arturs-lab/basis108/commercial_version/applefritter/resources/oldcomputer.info/revw.pdf

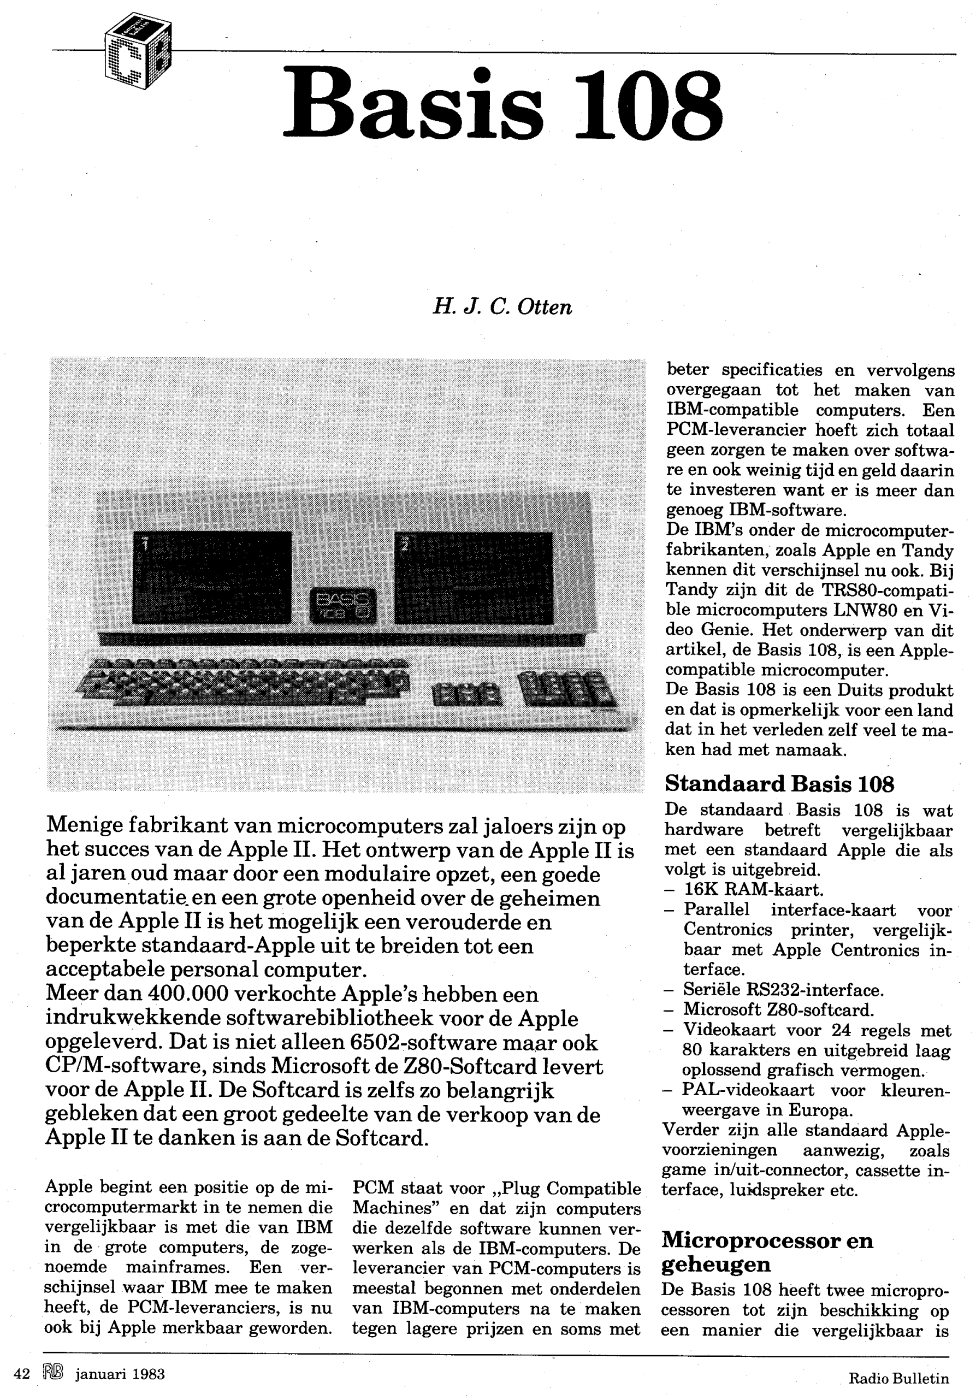
[picture p13: figure]

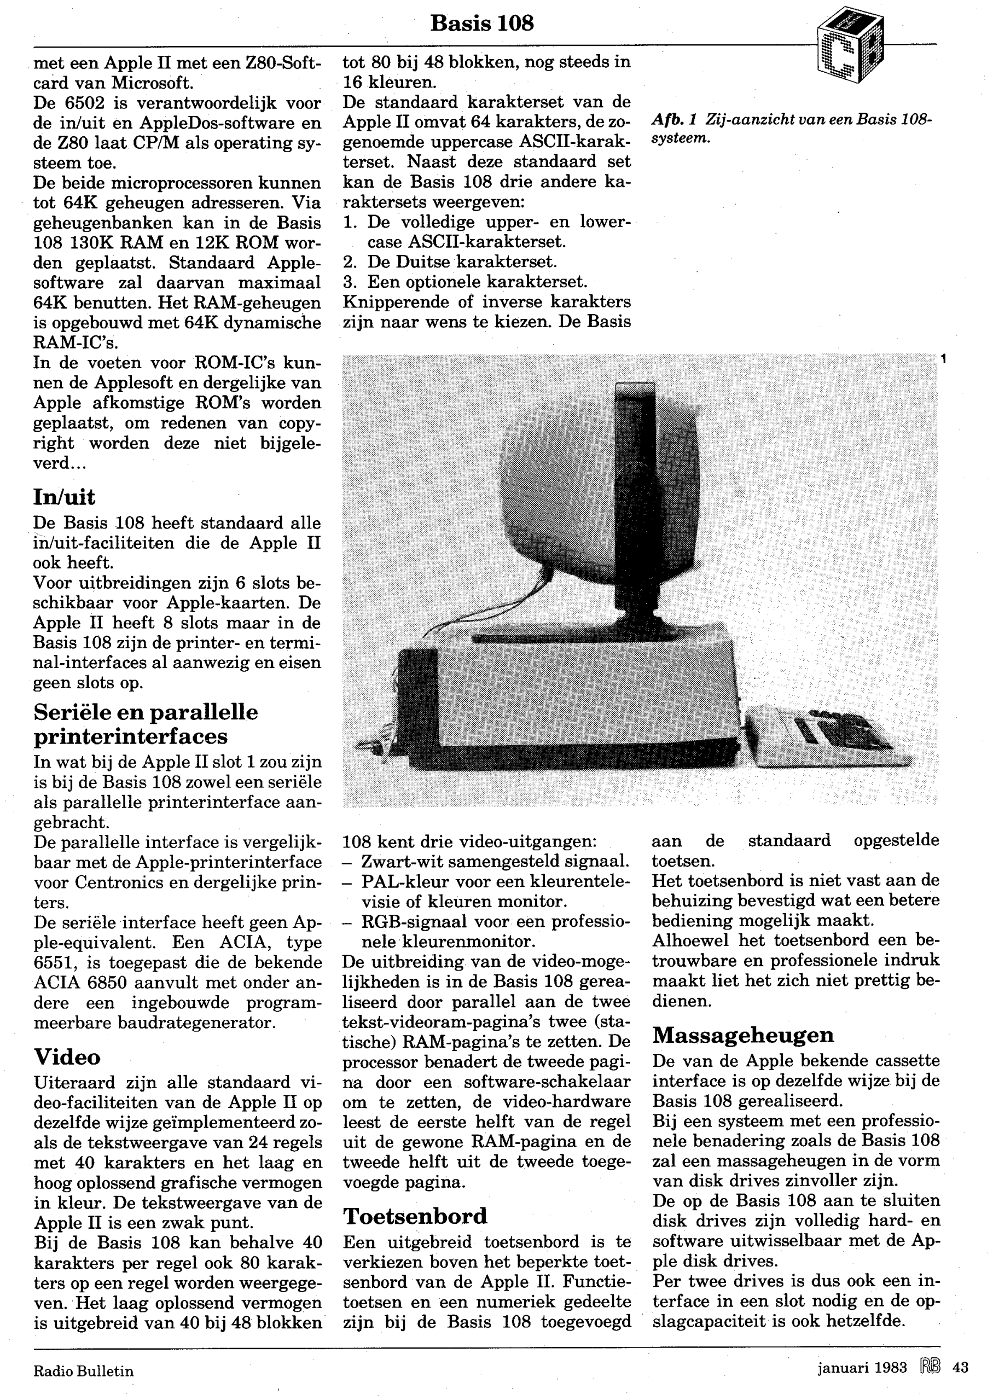
[picture p14: figure]

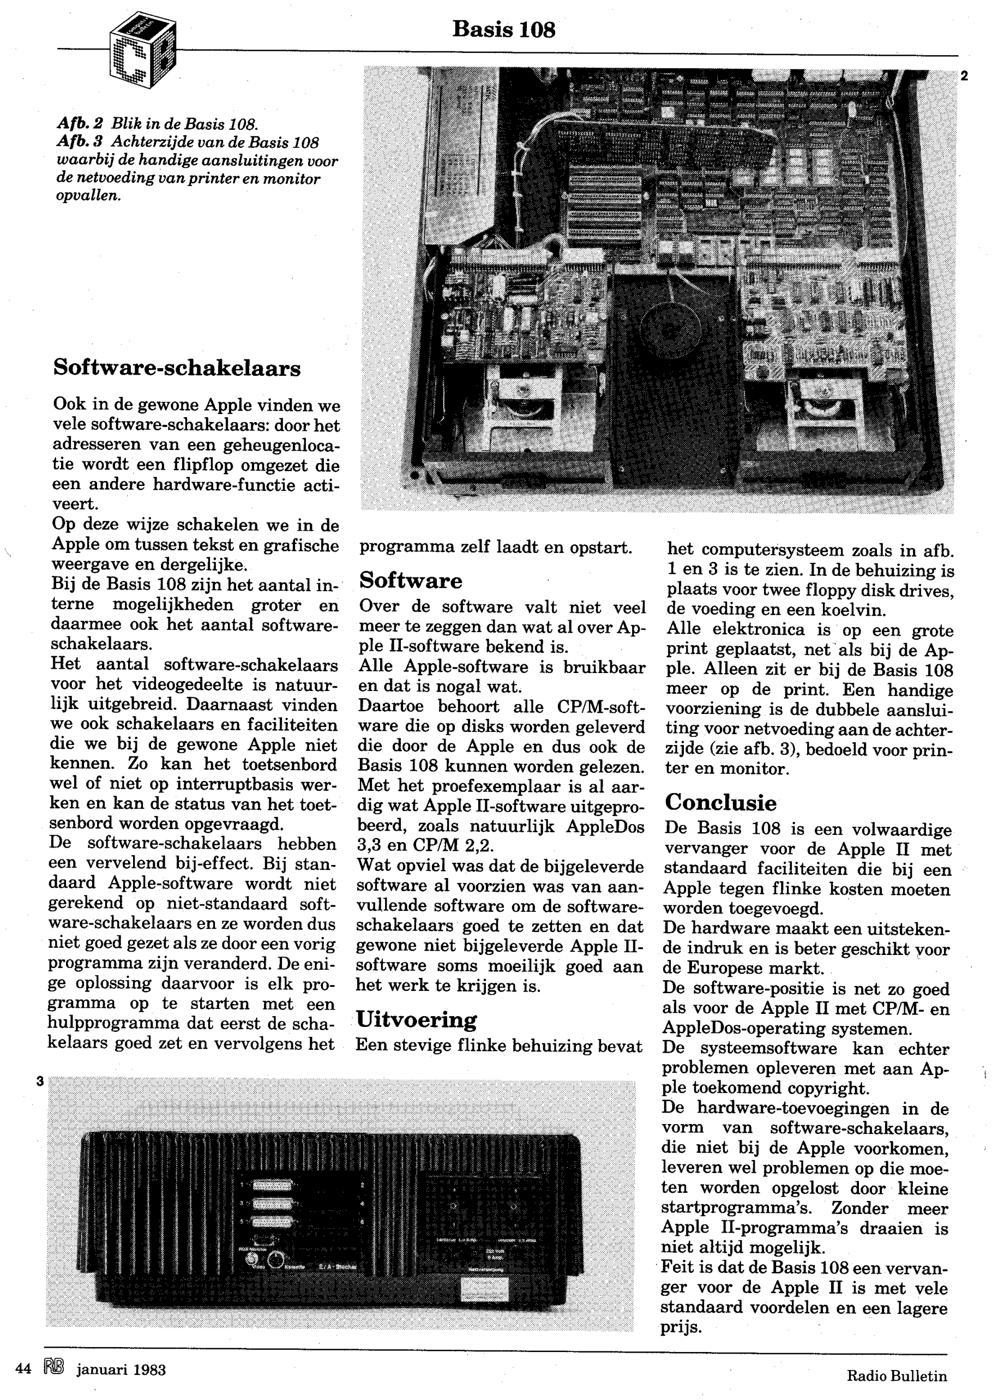
[picture p15: figure]
