arturs-lab/basis108/commercial_version/applefritter/Basis 108 Clone _ Applefritter_files/b108_07.JPG

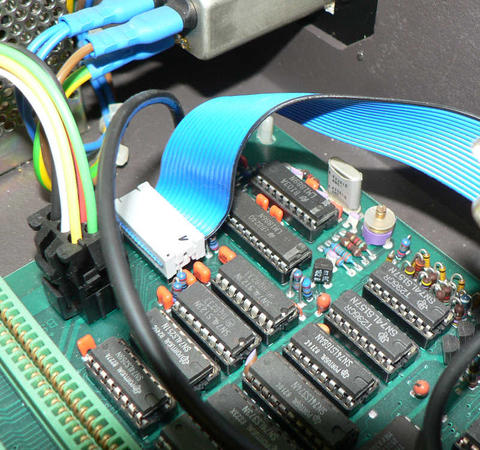
commercial_version/applefritter/Basis 108 Clone _ Applefritter_files/b108_07.JPG
