arturs-lab/basis108/commercial_version/applefritter/Basis 108 Clone _ Applefritter_files/Basis-108-EPROMs_and_Switch_0.jpg

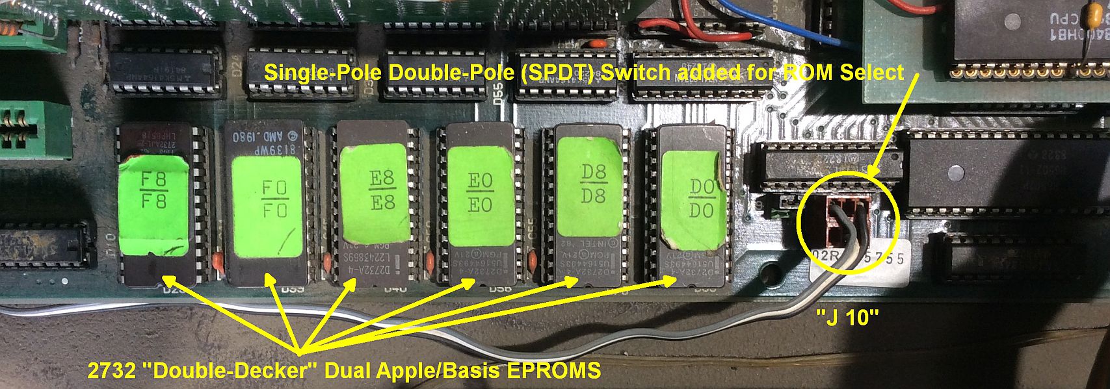
commercial_version/applefritter/Basis 108 Clone _ Applefritter_files/Basis-108-EPROMs_and_Switch_0.jpg
