arturs-lab/basis108/commercial_version/applefritter/Basis 108 Clone _ Applefritter_files/Basis-108-Interior-All-Ann1.jpg

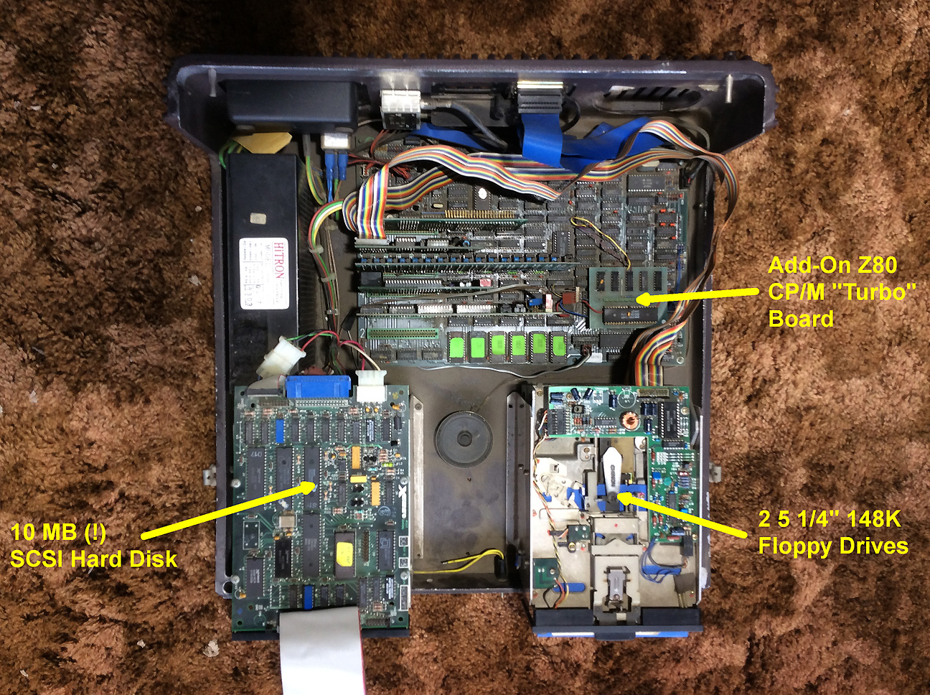
commercial_version/applefritter/Basis 108 Clone _ Applefritter_files/Basis-108-Interior-All-Ann1.jpg
