arturs-lab/basis108/commercial_version/images/FB_IMG_1675830168287.jpg

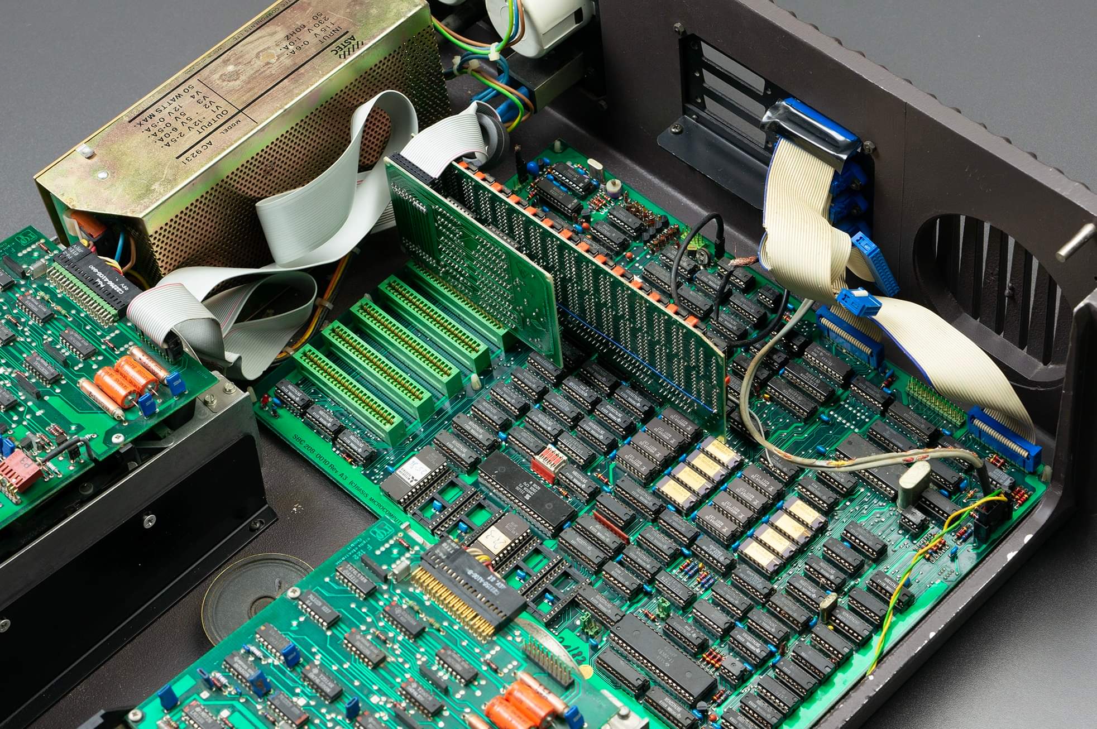
commercial_version/images/FB_IMG_1675830168287.jpg
