arturs-lab/basis108/commercial_version/images/FB_IMG_1675830313314.jpg

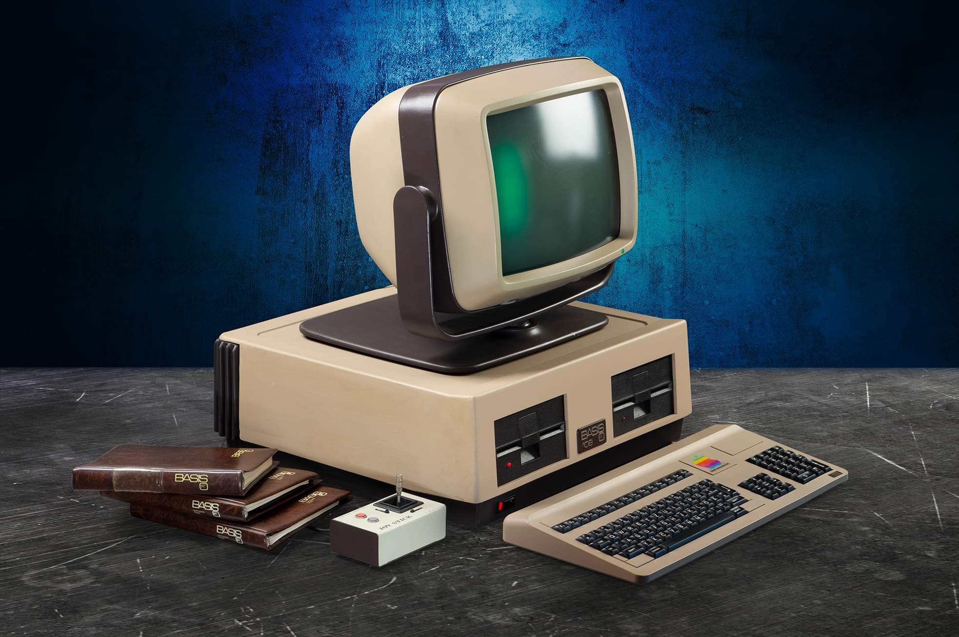
commercial_version/images/FB_IMG_1675830313314.jpg
