arturs-lab/basis108/commercial_version/images/FB_IMG_1675830322174.jpg

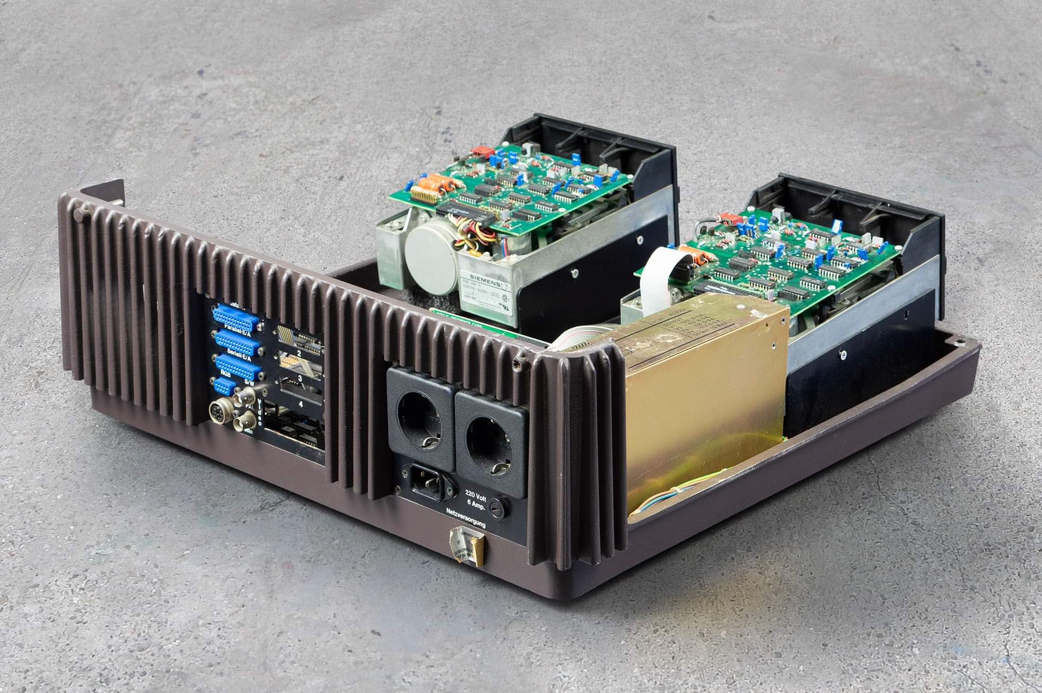
commercial_version/images/FB_IMG_1675830322174.jpg
