arturs-lab/basis108/floppy_controller/AppleBox - Ehring FDC4 Diskcontroller_files/FDC4Bild.jpg

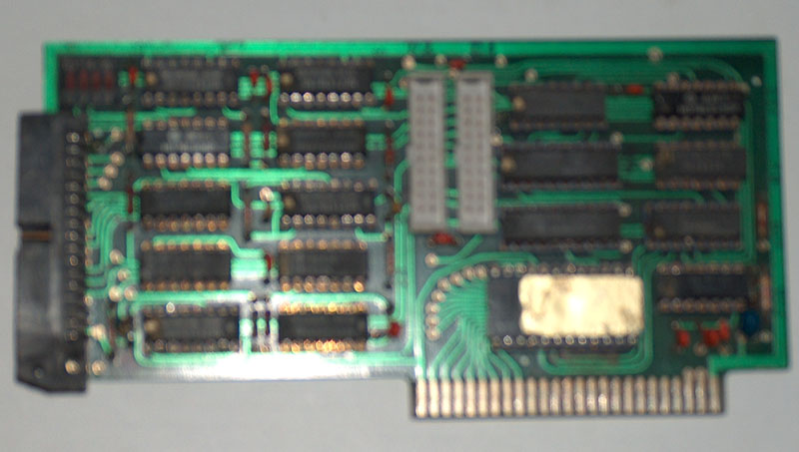
floppy_controller/AppleBox - Ehring FDC4 Diskcontroller_files/FDC4Bild.jpg
