arturs-lab/basis108/floppy_controller/AppleBox - Ehring FDC4 Diskcontroller_files/FDC4Schaltplan.jpg

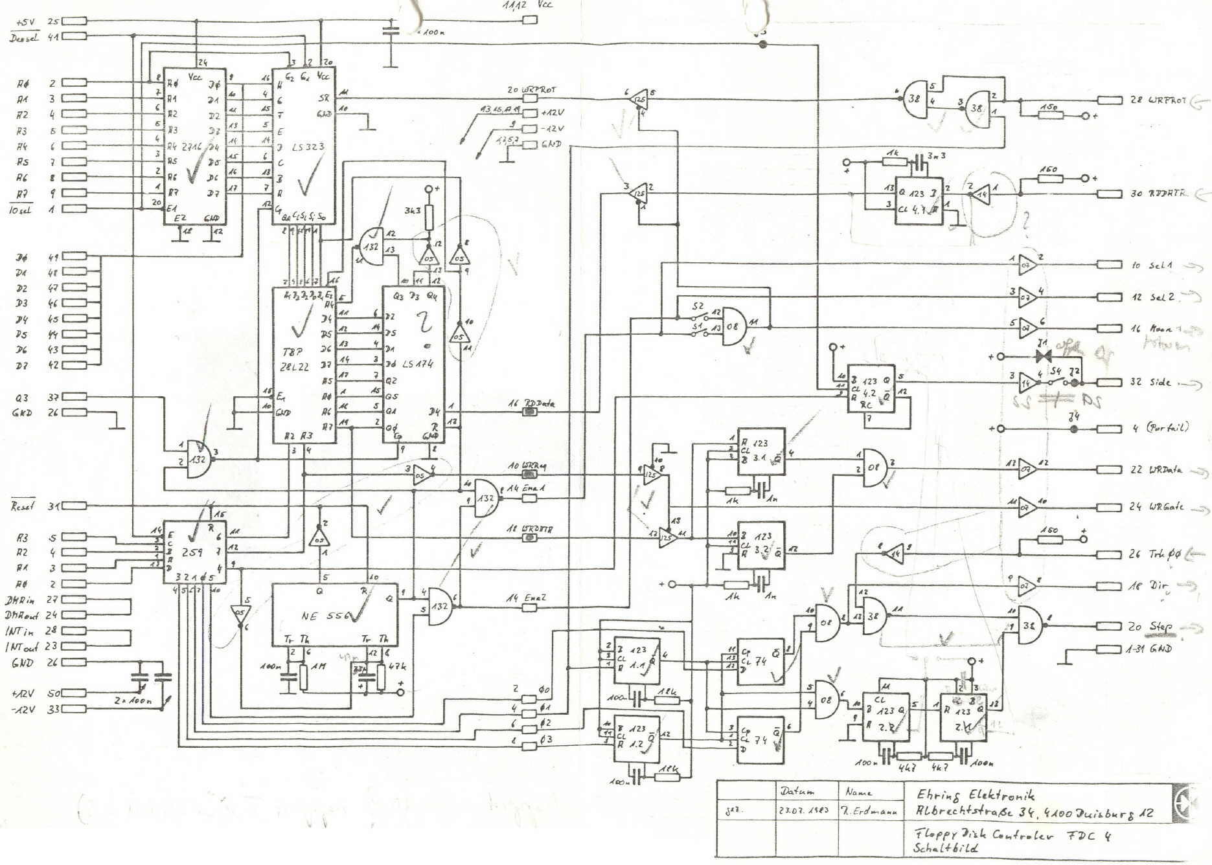
floppy_controller/AppleBox - Ehring FDC4 Diskcontroller_files/FDC4Schaltplan.jpg
