arturs-lab/basis108/floppy_controller/AppleBox - Ehring FDC4 Diskcontroller_files/page004.jpg

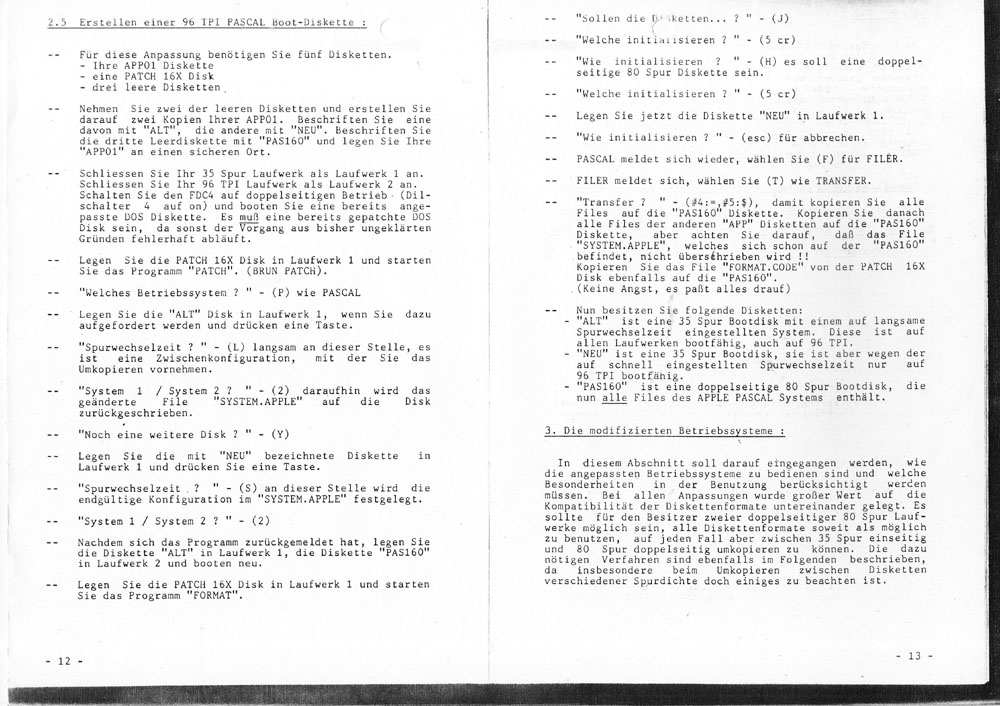
floppy_controller/AppleBox - Ehring FDC4 Diskcontroller_files/page004.jpg
