arturs-lab/basis108/floppy_controller/AppleBox - Ehring FDC4 Diskcontroller_files/page014.jpg

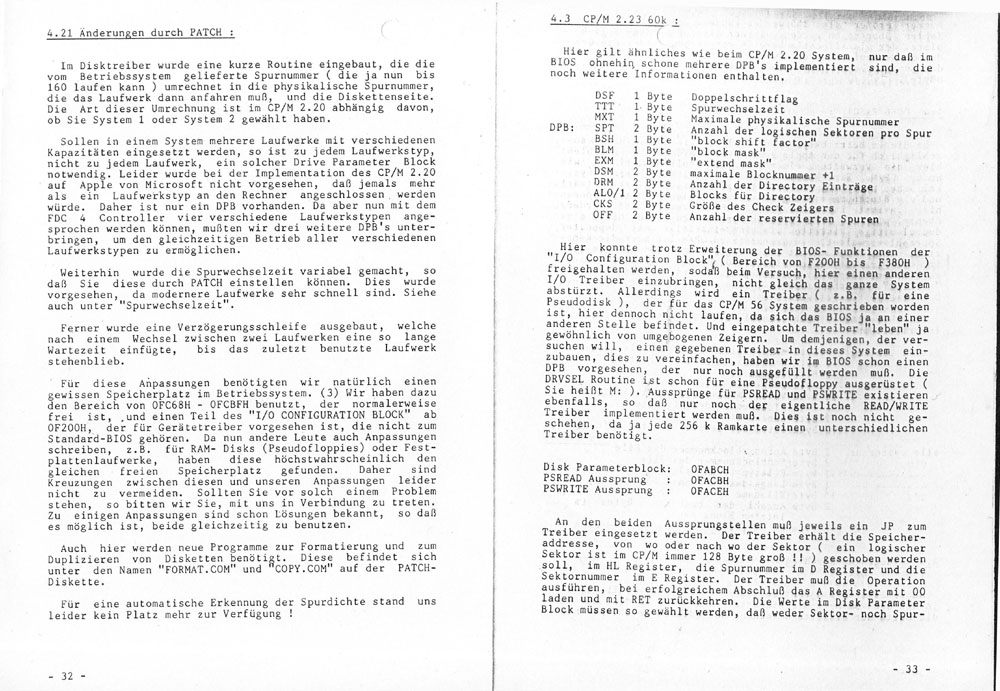
floppy_controller/AppleBox - Ehring FDC4 Diskcontroller_files/page014.jpg
