arturs-lab/basis108/floppy_controller/images/20250504_134716.jpg

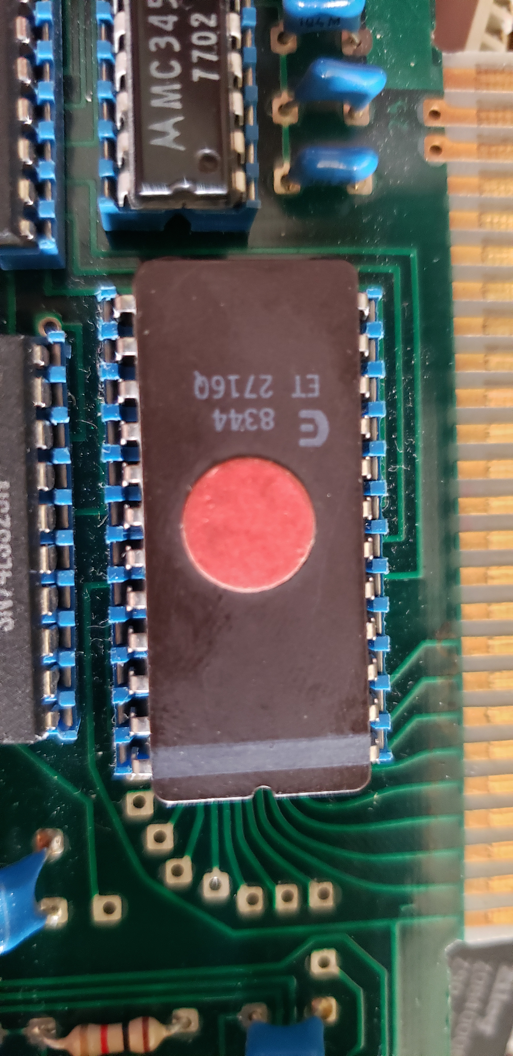
floppy_controller/images/20250504_134716.jpg
