arturs-lab/basis108/floppy_controller/images/20250512_174314.jpg

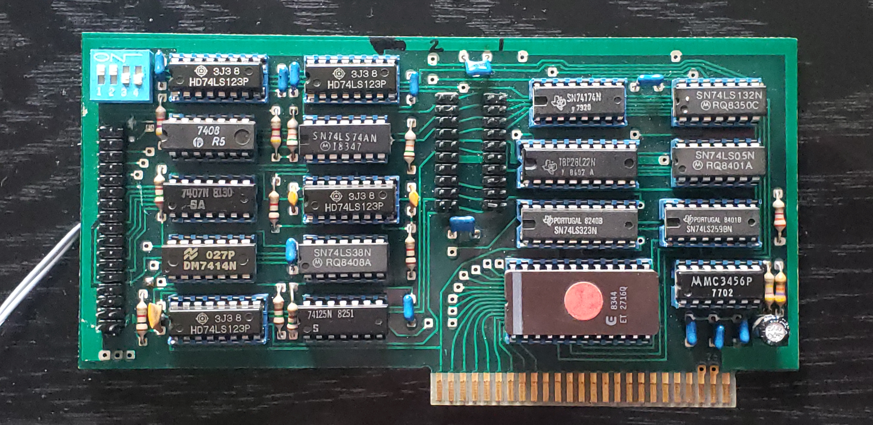
floppy_controller/images/20250512_174314.jpg
