arturs-lab/basis108/floppy_controller/images/20250512_174329.jpg

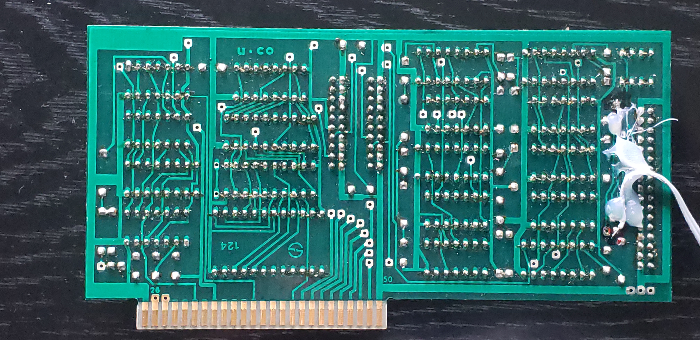
floppy_controller/images/20250512_174329.jpg
