arturs-lab/basis108/floppy_drive/images/20230804_221040.jpg

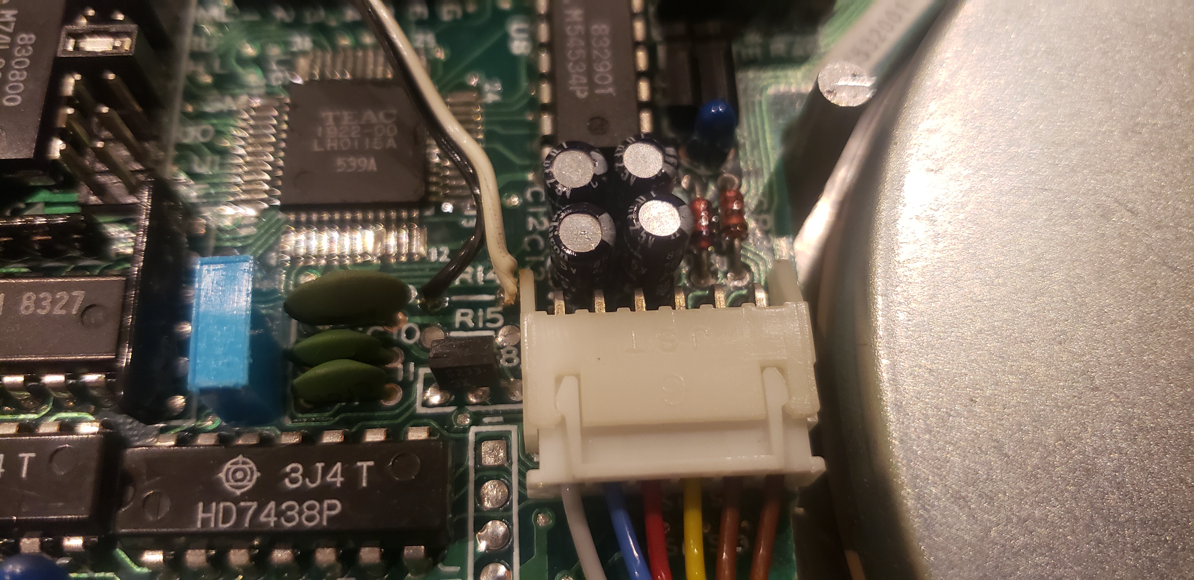
floppy_drive/images/20230804_221040.jpg
