arturs-lab/basis108/floppy_drive/images/20230804_221119.jpg

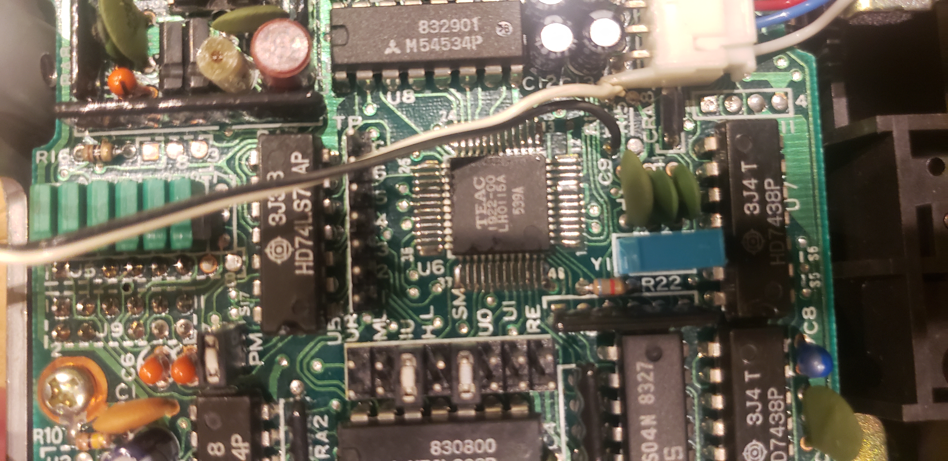
floppy_drive/images/20230804_221119.jpg
