arturs-lab/basis108/floppy_drive/images/20230804_221159.jpg

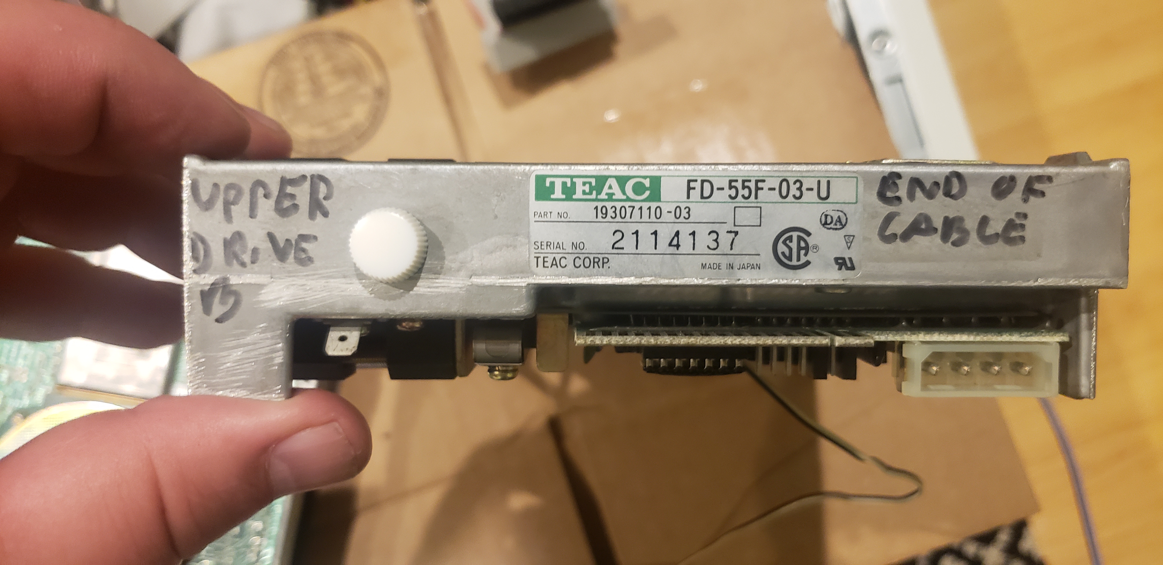
floppy_drive/images/20230804_221159.jpg
