arturs-lab/basis108/floppy_drive/images/20230804_221204.jpg

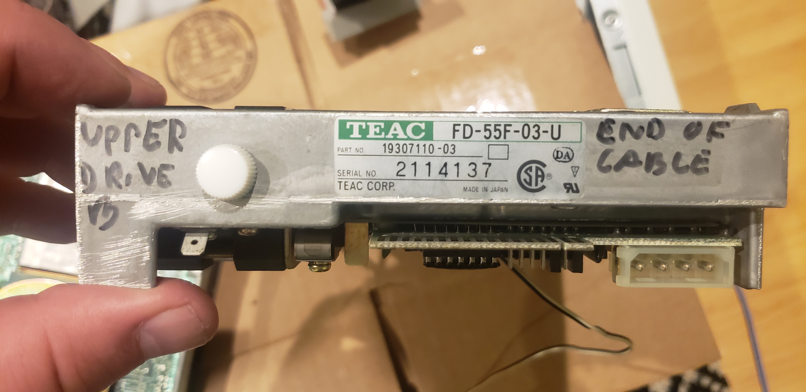
floppy_drive/images/20230804_221204.jpg
