arturs-lab/basis108/floppy_drive/images/20250512_160746.jpg

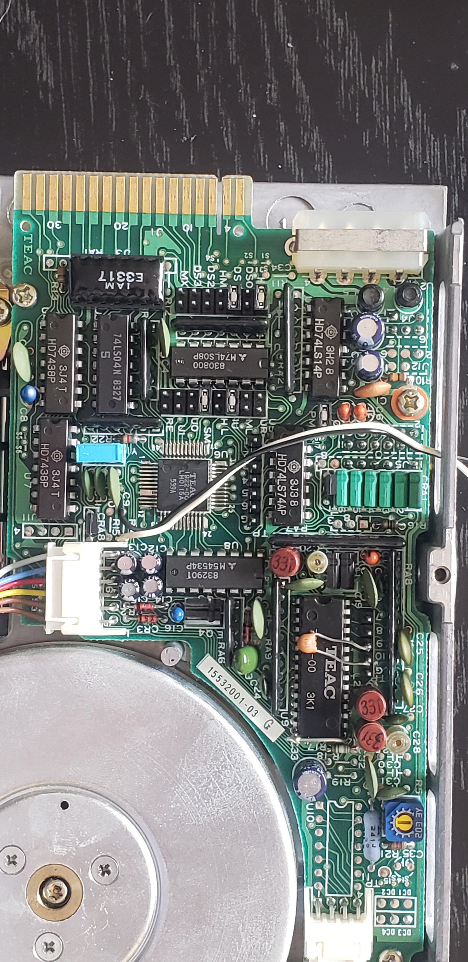
floppy_drive/images/20250512_160746.jpg
