arturs-lab/basis108/floppy_drive/images/20250512_160801.jpg

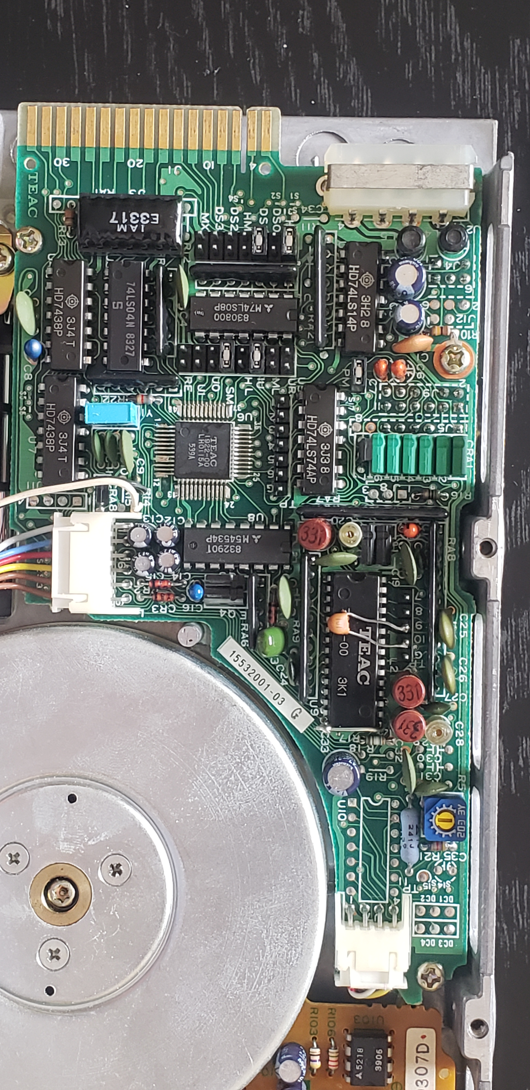
floppy_drive/images/20250512_160801.jpg
