arturs-lab/basis108/floppy_drive/images/20250512_160935.jpg

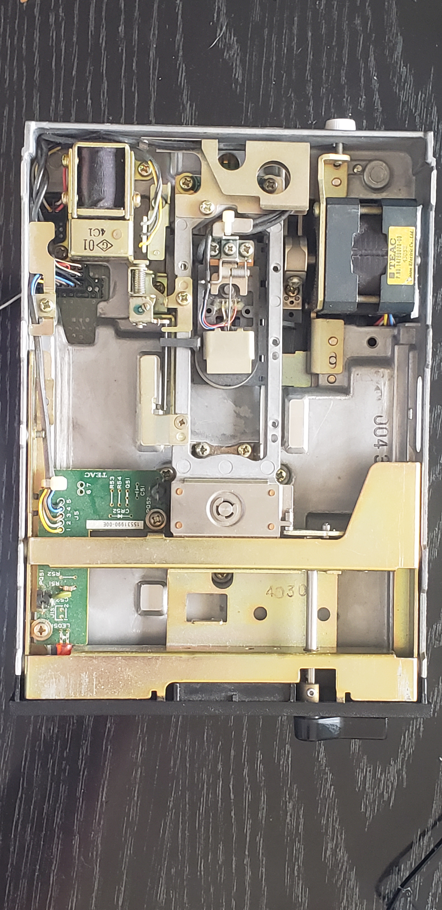
floppy_drive/images/20250512_160935.jpg
