arturs-lab/basis108/floppy_drive/images/20250512_160948.jpg

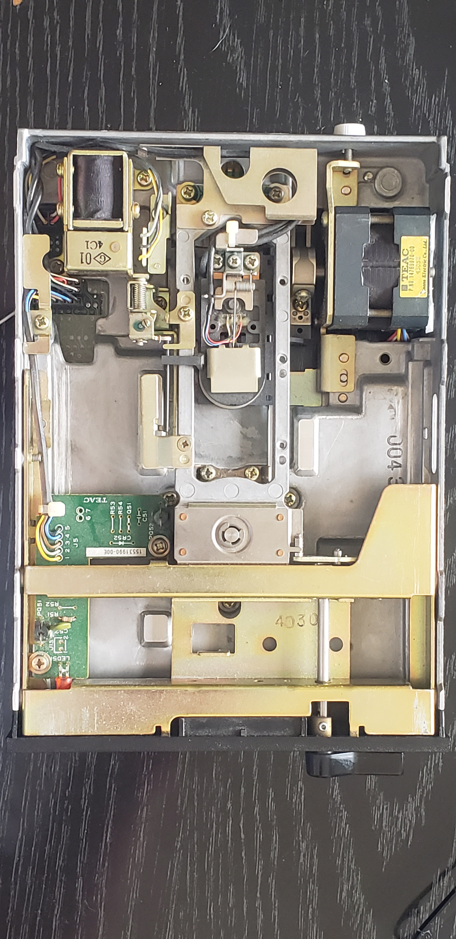
floppy_drive/images/20250512_160948.jpg
