arturs-lab/basis108/floppy_drive/images/data timing/000_data_line_after_start.BMP

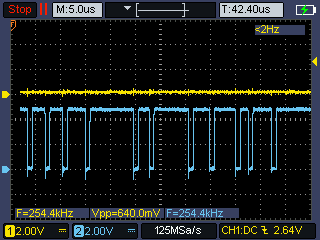
floppy_drive/images/data timing/000_data_line_after_start.BMP
