arturs-lab/basis108/floppy_drive/images/data timing/001_data_line_4us.BMP

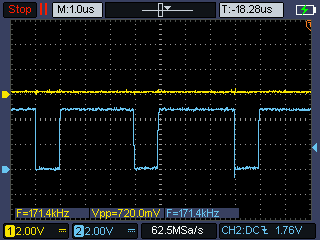
floppy_drive/images/data timing/001_data_line_4us.BMP
