arturs-lab/basis108/floppy_drive/images/data timing/002_data_line_7.5us.BMP

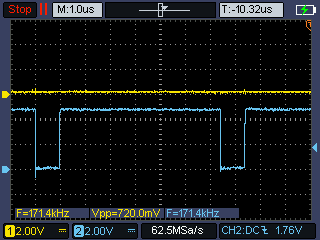
floppy_drive/images/data timing/002_data_line_7.5us.BMP
