arturs-lab/basis108/floppy_drive/images/data timing/003_data_line_11.5us.BMP

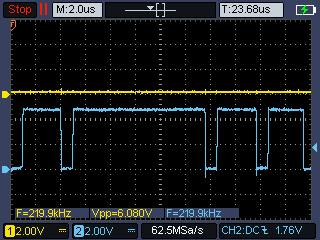
floppy_drive/images/data timing/003_data_line_11.5us.BMP
