arturs-lab/basis108/floppy_drive/images/data timing/004_data_line_12.5Msps.BMP

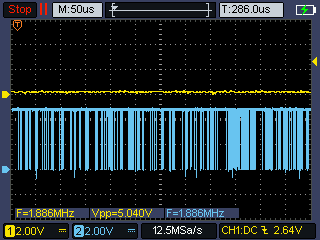
floppy_drive/images/data timing/004_data_line_12.5Msps.BMP
