arturs-lab/basis108/floppy_drive/images/data timing/005_data_line_2.5Msps.BMP

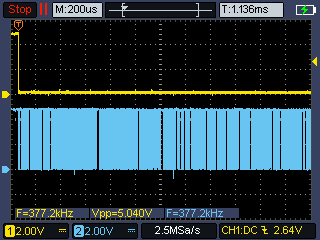
floppy_drive/images/data timing/005_data_line_2.5Msps.BMP
