arturs-lab/basis108/floppy_drive/images/data timing/006_data_line_1.25Msps.BMP

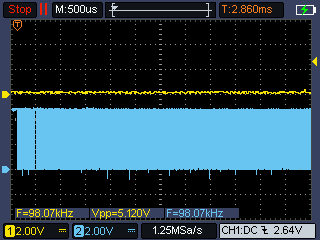
floppy_drive/images/data timing/006_data_line_1.25Msps.BMP
