arturs-lab/basis108/floppy_drive/images/data timing/008_index.BMP

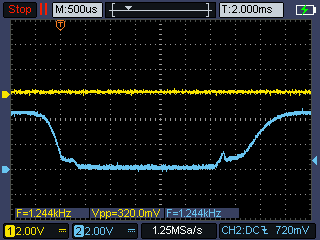
floppy_drive/images/data timing/008_index.BMP
