arturs-lab/basis108/floppy_drive/images/data timing/009_index.BMP

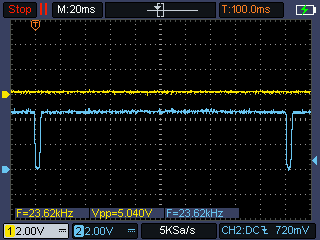
floppy_drive/images/data timing/009_index.BMP
