arturs-lab/basis108/floppy_drive/images/data timing/gotek/002_trying_to_switch_to_drive_b.BMP

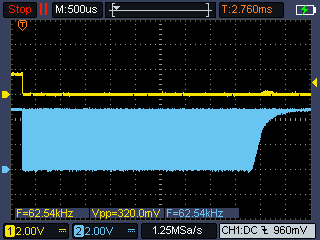
floppy_drive/images/data timing/gotek/002_trying_to_switch_to_drive_b.BMP
