arturs-lab/basis108/floppy_drive/images/data timing/gotek/003_data_spacing_zeroed_image.BMP

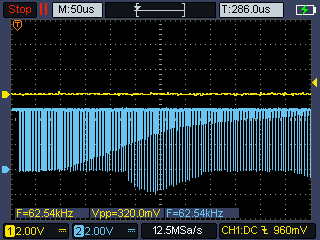
floppy_drive/images/data timing/gotek/003_data_spacing_zeroed_image.BMP
