arturs-lab/basis108/floppy_drive/images/data timing/gotek/004_data_spacing_zeroed_image.BMP

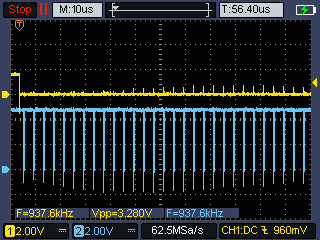
floppy_drive/images/data timing/gotek/004_data_spacing_zeroed_image.BMP
