arturs-lab/basis108/main_board/images/20240120_193323.jpg

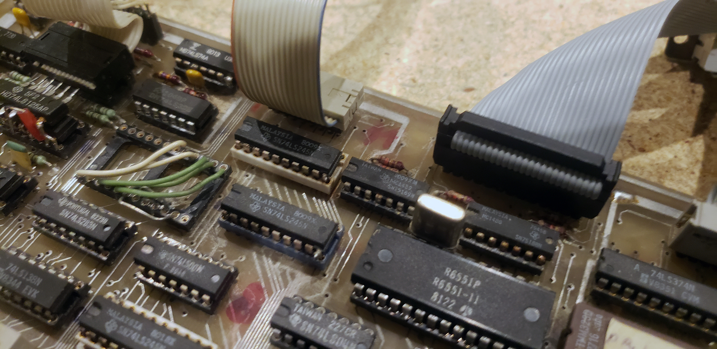
main_board/images/20240120_193323.jpg
