arturs-lab/basis108/main_board/images/20240120_193327.jpg

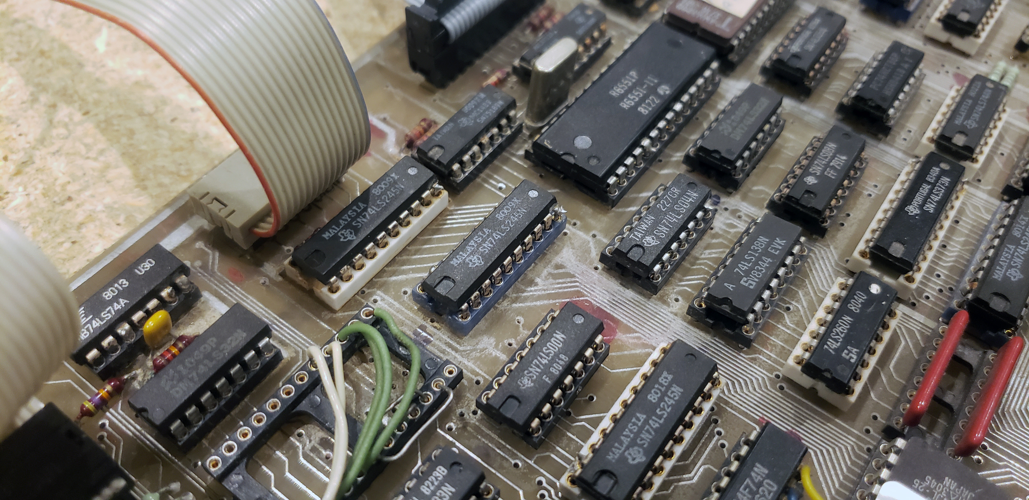
main_board/images/20240120_193327.jpg
