arturs-lab/basis108/main_board/images/20240305_235706.jpg

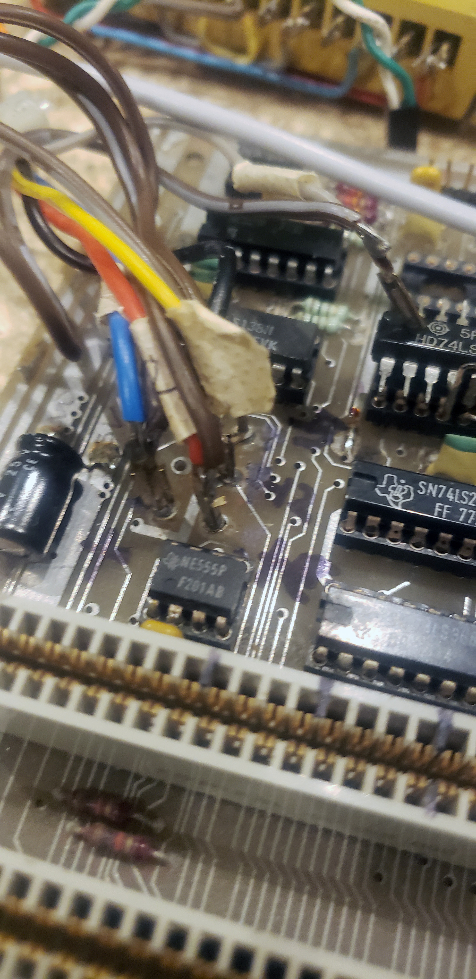
main_board/images/20240305_235706.jpg
