arturs-lab/basis108/main_board/images/20240305_235730.jpg

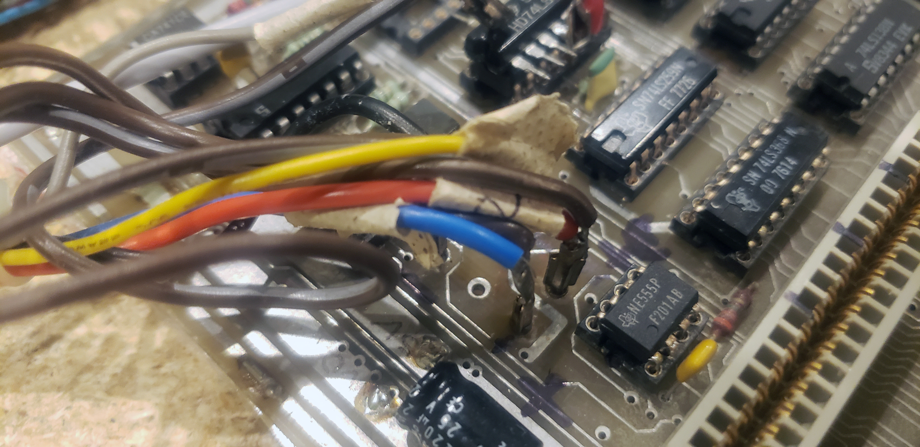
main_board/images/20240305_235730.jpg
