arturs-lab/basis108/main_board/images/20240308_193422.jpg

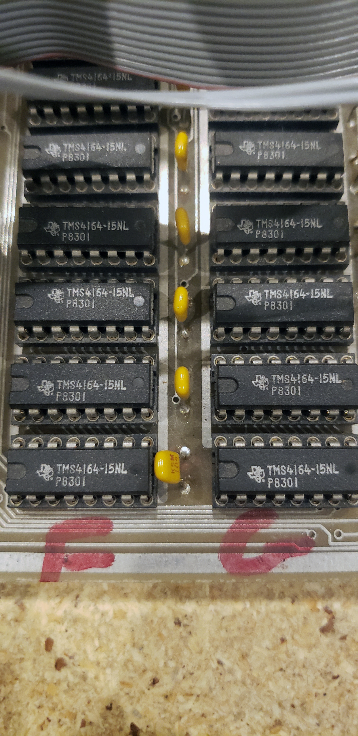
main_board/images/20240308_193422.jpg
