arturs-lab/basis108/main_board/images/20250504_134456.jpg

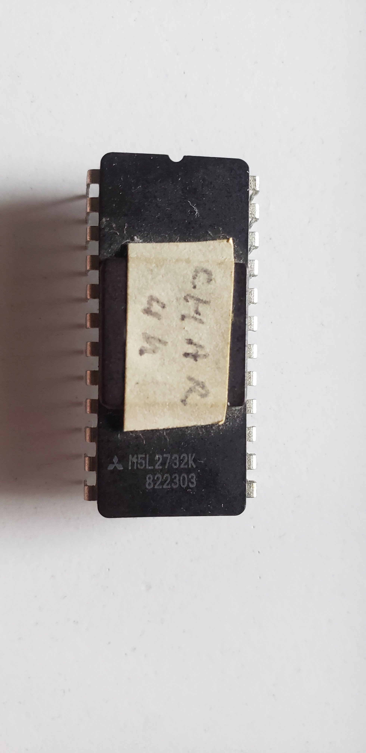
main_board/images/20250504_134456.jpg
