arturs-lab/basis108/main_board/images/20250504_134831.jpg

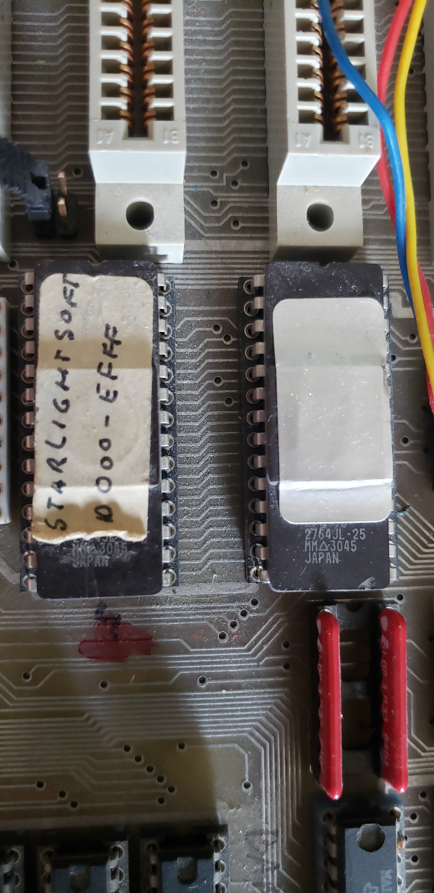
main_board/images/20250504_134831.jpg
