arturs-lab/basis108/main_board/images/20250504_135722.jpg

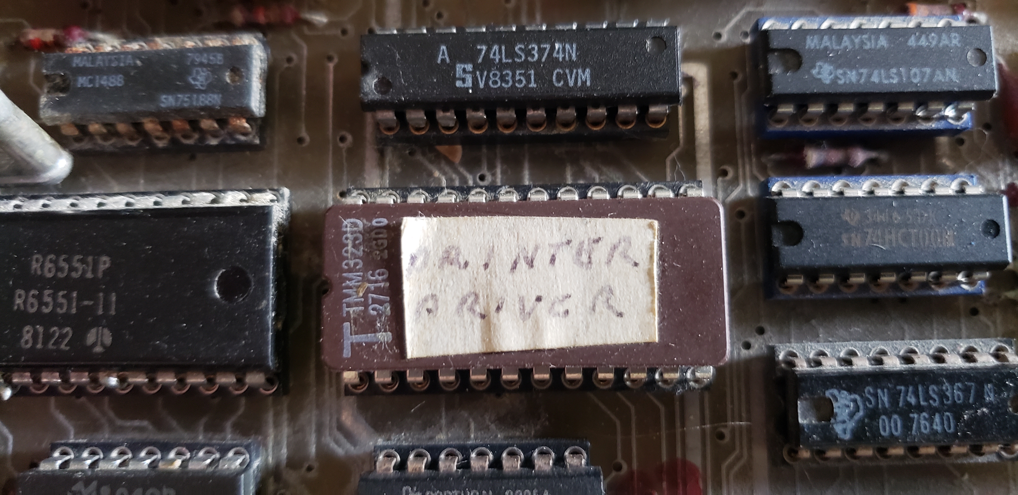
main_board/images/20250504_135722.jpg
